satomm1/mattbot_record/firmware/ProjectSource/main.c

/****************************************************************************
 Module
     main.c
 Description
     starter main() function for Events and Services Framework applications
 Notes

*****************************************************************************/
#include <stdint.h>
#include <stdbool.h>
#include <stdio.h>
#include <assert.h>

#include "ES_Configure.h"
#include "ES_Framework.h"
#include "ES_Port.h"


void main(void)
{
  ES_Return_t ErrorType = Success;

  _HW_PIC32Init(); // basic PIC hardware init
  // Your hardware initialization function calls go here

  _PBCLK_Init(); // Set PBLCKs to starting desired frequency

  // now initialize the Events and Services Framework and start it running
  ErrorType = ES_Initialize(ES_Timer_RATE_1mS);
  if (ErrorType == Success)
  {
    ErrorType = ES_Run();
  }
  //if we got to here, there was an error
  switch (ErrorType)
  {
    case FailedPost:
    {
      ErrorType = 0; // a hack to get a readable assert message
      assert( FailedPost == ErrorType );
      //DB_printf("Failed on attempt to Post\n");
    }
    break;
    case FailedPointer:
    {
      ErrorType = 0; // a hack to get a readable assert message
      assert( FailedPointer  == ErrorType );
//      DB_printf("Failed on NULL pointer\n");
    }
    break;
    case FailedInit:
    {
      ErrorType = 0; // a hack to get a readable assert message
      assert( FailedInit  == ErrorType );
//      DB_printf("Failed Initialization\n");
    }
    break;
    default:
    {
      ErrorType = 0; // a hack to get a readable assert message
      assert( FailedOther  == ErrorType );
//      DB_printf("Other Failure\n");
    }
    break;
  }
  for ( ; ;)
  {
    ;
  }
}
